BenSeverson/RocketAltimeter/firmware/AltimeterHID/io_cfg.h

/*********************************************************************
 *
 *                Microchip USB C18 Firmware Version 1.2
 *
 *********************************************************************
 * FileName:        io_cfg.h
 * Dependencies:    See INCLUDES section below
 * Processor:       PIC18
 * Compiler:        C18 3.11+
 * Company:         Microchip Technology, Inc.
 *
 * Software License Agreement
 *
 * The software supplied herewith by Microchip Technology Incorporated
 * (the “Company”) for its PICmicro® Microcontroller is intended and
 * supplied to you, the Company’s customer, for use solely and
 * exclusively on Microchip PICmicro Microcontroller products. The
 * software is owned by the Company and/or its supplier, and is
 * protected under applicable copyright laws. All rights are reserved.
 * Any use in violation of the foregoing restrictions may subject the
 * user to criminal sanctions under applicable laws, as well as to
 * civil liability for the breach of the terms and conditions of this
 * license.
 *
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
 * Author               Date        Comment
 *~~~~~~~~~~~~~~~~~~~~~~~~~~~~~~~~~~~~~~~~~~~~~~~~~~~~~~~~~~~~~~~~~~~~
 * Rawin Rojvanit       11/19/04    Original.
 * Rawin Rojvanit       05/14/07    Added pin mapping for PIC18F87J50
 *									FS USB Plug In Module board.
 ********************************************************************/

#ifndef IO_CFG_H
#define IO_CFG_H

/** I N C L U D E S *************************************************/
#include "autofiles\usbcfg.h"

/** T R I S *********************************************************/
#define INPUT_PIN           1
#define OUTPUT_PIN          0

/** U S B ***********************************************************/
#define tris_usb_bus_sense  TRISAbits.TRISA1    // Input

#if defined(USE_USB_BUS_SENSE_IO)
#define usb_bus_sense       PORTAbits.RA1
#else
#define usb_bus_sense       1
#endif

// External Transceiver Interface
#define tris_usb_vpo        TRISBbits.TRISB3    // Output
#define tris_usb_vmo        TRISBbits.TRISB2    // Output
#define tris_usb_rcv        TRISAbits.TRISA4    // Input
#define tris_usb_vp         TRISCbits.TRISC5    // Input
#define tris_usb_vm         TRISCbits.TRISC4    // Input
#define tris_usb_oe         TRISCbits.TRISC1    // Output

#define tris_usb_suspnd     TRISAbits.TRISA3    // Output

/** L E D ***********************************************************/
#define mInitAllLEDs()      LATC &= 0xFC; TRISC &= 0xFC;

#define mLED_1              LATCbits.LATC0
#define mLED_2              LATCbits.LATC1

#define mLED_1_On()         mLED_1 = 1;
#define mLED_2_On()         mLED_2 = 1;

#define mLED_1_Off()        mLED_1 = 0;
#define mLED_2_Off()        mLED_2 = 0;

#define mLED_1_Toggle()     mLED_1 = !mLED_1;
#define mLED_2_Toggle()     mLED_2 = !mLED_2;

/** S W I T C H *****************************************************/
#define mInitAllSwitches()  TRISBbits.TRISB2=1;TRISBbits.TRISB3=1;
#define mInitSwitch1()      TRISBbits.TRISB2=1;
#define mInitSwitch2()      TRISBbits.TRISB3=1;
#define sw1                 PORTBbits.RB4
#define sw2                 PORTBbits.RB5

#endif //IO_CFG_H
