BenSeverson/RocketAltimeter/firmware/AltimeterHID/user/lut.h

#pragma romdata

// Altitudes in feet corresponding to ADC values for pressure sensor at 0-5V ref
// need to subtract 112 from ADC value before looking up
rom const unsigned int altitudeLUT[725] = {
36019,
35920,
35821,
35722,
35624,
35526,
35429,
35332,
35235,
35139,
35043,
34947,
34852,
34757,
34662,
34568,
34474,
34381,
34287,
34195,
34102,
34010,
33918,
33826,
33735,
33644,
33553,
33463,
33373,
33283,
33194,
33105,
33016,
32928,
32839,
32752,
32664,
32577,
32489,
32403,
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
};

#pragma code
